RT-CUSTOMZ/LEDmePlay/include/Pacer_Data.hpp

#ifndef PACER_MUSIC_HPP
#define PACER_MUSIC_HPP

#include <Arduino.h>


#define STOP 0
#define PACER_ATE_PILL 1 // Noise names
#define PACER_ATE_SUPERPILL 2
#define BADDIESFLEE_MELODY 3
#define GAMEOVER_NOISE 4
#define BONUSITEM_JINGLE 5
#define OPENING_JINGLE 6
#define ADDITIONALLIFE_JINGLE 7
#define BADDIECAUGHT_JINGLE 8


// 0 - Orange
// 1 - Red
// 2 - Black
// 3 - White
// 4 - Yellow
const uint8_t titleImg[] PROGMEM =
    {2, 1, 1, 1, 1, 1, 1, 1, 1, 1, 1, 1, 1, 1, 1, 1, 1, 1, 1, 1, 1, 1, 1, 1, 1, 1, 1, 1, 1, 1, 1, 2,
     1, 0, 0, 0, 0, 0, 0, 0, 0, 0, 0, 0, 0, 0, 0, 0, 0, 0, 0, 0, 0, 0, 0, 0, 0, 0, 0, 0, 0, 0, 0, 1,
     1, 0, 3, 3, 3, 3, 0, 0, 0, 3, 0, 0, 0, 0, 3, 3, 3, 0, 0, 3, 3, 3, 3, 3, 0, 3, 3, 3, 3, 0, 0, 1,
     1, 3, 4, 4, 4, 4, 3, 0, 3, 4, 0, 0, 0, 3, 3, 4, 4, 4, 3, 4, 4, 4, 4, 4, 3, 4, 4, 4, 4, 0, 0, 1,
     1, 3, 4, 4, 4, 4, 4, 0, 3, 4, 2, 0, 3, 4, 4, 4, 4, 4, 3, 4, 4, 4, 4, 4, 3, 4, 4, 4, 4, 4, 0, 1,
     1, 3, 4, 4, 2, 4, 4, 3, 4, 4, 4, 2, 3, 4, 4, 4, 2, 2, 3, 4, 4, 2, 2, 2, 3, 4, 4, 2, 4, 4, 0, 1,
     1, 3, 4, 4, 4, 4, 4, 3, 4, 4, 4, 2, 3, 4, 4, 2, 0, 0, 3, 4, 4, 4, 4, 4, 3, 4, 4, 4, 4, 0, 0, 1,
     1, 3, 4, 4, 4, 2, 3, 4, 4, 2, 4, 4, 3, 4, 4, 4, 0, 0, 3, 4, 4, 4, 2, 2, 3, 4, 4, 4, 2, 2, 0, 1,
     1, 3, 4, 4, 4, 2, 3, 4, 4, 4, 4, 4, 2, 4, 4, 4, 4, 4, 3, 4, 4, 4, 4, 4, 2, 4, 4, 4, 4, 2, 0, 1,
     1, 0, 4, 4, 4, 2, 4, 4, 4, 4, 4, 4, 4, 2, 4, 4, 4, 4, 2, 4, 4, 4, 4, 4, 2, 4, 4, 4, 4, 4, 0, 1,
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
    0, 1, 1, 1, 4, 5, 3, 3, 1, 0,
    0, 1, 1, 1, 6, 7, 1, 1, 1, 0,
    0, 1, 1, 1, 1, 1, 3, 3, 1, 0,
    0, 1, 1, 1, 3, 3, 1, 1, 1, 0,
    0, 3, 3, 3, 1, 1, 1, 8, 3, 0,
    0, 3, 3, 1, 1, 1, 1, 3, 3, 0,
    0, 0, 0, 9, 9, 9, 9, 0, 0, 0

};

#endif /* PACER_MUSIC_HPP */
